kbsriram/a-tiny-sieve/code/02/rpi/pins.py

PIN_REQ = 14
PIN_VOTE = 15
PIN_SDA = 16
PIN_SCL = 17
